7vgn/MacroPad/Software/res/macropad.png

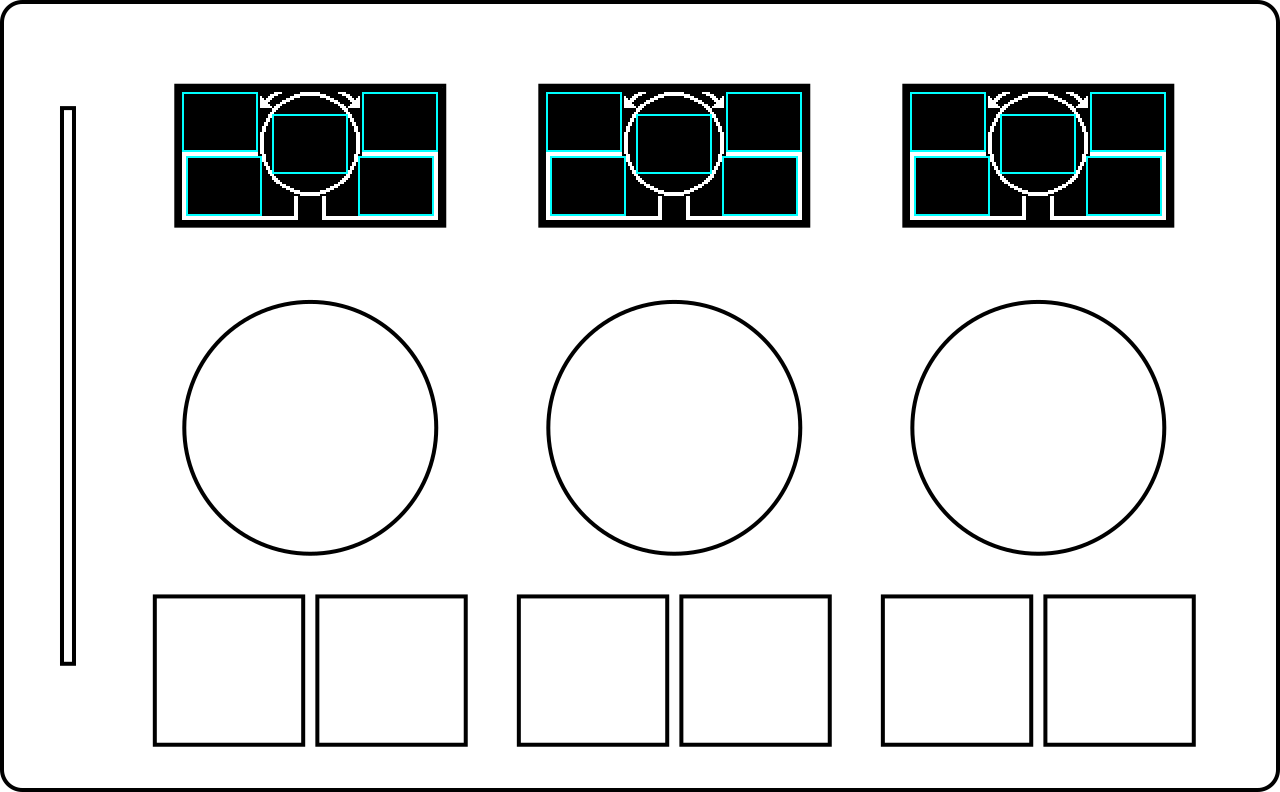
Software/res/macropad.png
