7vgn/MacroPad/Firmware/src/settingstools.cpp

/**
 * \file settingstools.cpp
 * Implementation for settingstools.h
 */

#include<cstdio>
#include"tusb.h"
#include"settingstools.h"

//-----------------------------------------------------------------------------
// Settings implementation

/**
 * \brief Default settings
 * \details These are the result of "macropad-cli -w defaultmp -b default.bin",
 * converted to a C array.
 */
static const uint8_t DEFAULT_SETTINGS[]  = {
  0x00, 0x01, 0x00, 0x4d, 0x6f, 0x75, 0x73, 0x65, 0x00, 0x00, 0x00, 0x00, 0x00, 0x00, 0x00, 0x00,
  0x00, 0x00, 0x00, 0x00, 0x00, 0x00, 0x00, 0x00, 0x00, 0x00, 0x00, 0x00, 0x00, 0x00, 0x00, 0x00,
  0x00, 0x00, 0x00, 0x00, 0x00, 0x00, 0x00, 0x00, 0x00, 0x00, 0x00, 0x00, 0x00, 0x00, 0x00, 0x00,
  0x00, 0x00, 0x00, 0x00, 0x00, 0x00, 0x00, 0x00, 0x00, 0x00, 0x00, 0x00, 0x00, 0x00, 0x00, 0x00,
  0x00, 0x00, 0x00, 0x00, 0x00, 0x00, 0x00, 0x00, 0x00, 0x00, 0x00, 0x00, 0x00, 0x00, 0x00, 0x00,
  0x00, 0x00, 0x00, 0x00, 0x00, 0x00, 0x00, 0x00, 0x00, 0x00, 0x00, 0x00, 0x00, 0x00, 0x00, 0x00,
  0x00, 0x00, 0x00, 0x00, 0x00, 0x00, 0x00, 0x00, 0x00, 0x00, 0x00, 0x00, 0x00, 0x00, 0x00, 0x00,
  0x00, 0x00, 0x00, 0x00, 0x00, 0x00, 0x00, 0x00, 0x00, 0x00, 0x00, 0x00, 0x00, 0x00, 0x00, 0x00,
  0x00, 0x00, 0x00, 0x00, 0x00, 0x00, 0x00, 0x00, 0x00, 0x00, 0x00, 0x00, 0x00, 0x00, 0x00, 0x00,
  0x00, 0x00, 0x00, 0x00, 0x00, 0x00, 0x00, 0x00, 0x00, 0x00, 0x00, 0x00, 0x00, 0x00, 0x00, 0x00,
  0x00, 0x00, 0x00, 0x00, 0x00, 0x00, 0x00, 0x00, 0x00, 0x00, 0x00, 0x00, 0x00, 0x00, 0x00, 0x00,
  0x00, 0x00, 0x00, 0x00, 0x00, 0x00, 0x00, 0x00, 0x00, 0x00, 0x00, 0x00, 0x00, 0x00, 0x00, 0x00,
  0x00, 0x00, 0x00, 0x00, 0x00, 0x00, 0x00, 0x00, 0x00, 0x00, 0x00, 0x00, 0x00, 0x00, 0x00, 0x00,
  0x00, 0x00, 0x00, 0x00, 0x00, 0x00, 0x00, 0x00, 0x00, 0x00, 0x00, 0x00, 0x00, 0x00, 0x00, 0x00,
  0x00, 0x00, 0x00, 0x00, 0x00, 0x00, 0x00, 0x00, 0x00, 0x00, 0x00, 0x00, 0x00, 0x00, 0x00, 0x00,
  0x00, 0x00, 0x00, 0x00, 0x00, 0x00, 0x00, 0x00, 0x00, 0x00, 0x00, 0x00, 0x00, 0x00, 0x00, 0x00,
  0x00, 0x00, 0x00, 0x00, 0x00, 0x00, 0x00, 0x00, 0x00, 0x00, 0x00, 0x00, 0x00, 0x00, 0x00, 0x00,
  0x00, 0x00, 0x00, 0x00, 0x00, 0x00, 0x00, 0x00, 0x00, 0x00, 0x00, 0x00, 0x00, 0x00, 0x00, 0x00,
  0x00, 0x00, 0x00, 0x00, 0x00, 0x00, 0x00, 0x00, 0x00, 0x00, 0x00, 0x00, 0x00, 0x00, 0x00, 0x00,
  0x00, 0x00, 0x00, 0x00, 0x00, 0x00, 0x00, 0x00, 0x00, 0x00, 0x00, 0x00, 0x00, 0x00, 0x00, 0x00,
  0x00, 0x00, 0x00, 0x00, 0x00, 0x00, 0x00, 0x00, 0x00, 0x00, 0x00, 0x00, 0x00, 0x00, 0x00, 0x00,
  0x00, 0x00, 0x00, 0x00, 0x00, 0x00, 0x00, 0x00, 0x00, 0x0e, 0x00, 0x00, 0x00, 0x00, 0x00, 0x00,
  0x00, 0x00, 0x00, 0x00, 0x00, 0x00, 0x00, 0x00, 0x80, 0x3f, 0x00, 0x00, 0x00, 0x00, 0x00, 0x00,
  0x00, 0x00, 0x00, 0x00, 0x00, 0x00, 0x00, 0x00, 0xc0, 0x3f, 0x00, 0xf0, 0x1f, 0x00, 0x00, 0x00,
  0x00, 0x00, 0x00, 0x00, 0x00, 0x00, 0x00, 0x00, 0xe0, 0x7f, 0x00, 0x0f, 0xe0, 0x00, 0x00, 0x00,
  0x00, 0x00, 0x00, 0x00, 0x00, 0x00, 0x00, 0x00, 0xf0, 0xff, 0x80, 0x00, 0x00, 0x07, 0x00, 0x00,
  0x04, 0x00, 0x00, 0x00, 0x00, 0x00, 0x00, 0x00, 0xf8, 0xff, 0x61, 0x00, 0x00, 0x08, 0x00, 0x00,
  0x04, 0x00, 0x00, 0x00, 0x00, 0x00, 0x00, 0x00, 0xfc, 0xff, 0x1b, 0x00, 0x00, 0x10, 0x00, 0x00,
  0x04, 0x00, 0x00, 0x00, 0x00, 0x00, 0x00, 0x00, 0xfe, 0xff, 0x0f, 0x00, 0x00, 0x20, 0x00, 0x00,
  0x04, 0x00, 0x00, 0x00, 0x00, 0x00, 0x00, 0x00, 0xe7, 0xff, 0x0c, 0x00, 0x00, 0x20, 0x00, 0x00,
  0x04, 0x00, 0x00, 0x00, 0x00, 0x00, 0x00, 0x80, 0xc7, 0x7f, 0x1c, 0x00, 0x00, 0x40, 0x00, 0x00,
  0x02, 0x00, 0x00, 0x00, 0x00, 0x00, 0x00, 0xc0, 0x8f, 0x3f, 0x3e, 0x00, 0x00, 0x40, 0x00, 0x00,
  0x01, 0x00, 0x00, 0x00, 0x00, 0x00, 0x00, 0xe0, 0x1f, 0x1f, 0x7f, 0x00, 0x00, 0x80, 0x00, 0x00,
  0x01, 0x00, 0x00, 0x00, 0x00, 0x00, 0x00, 0xf0, 0x3f, 0x8e, 0xff, 0x00, 0x00, 0x80, 0x00, 0x80,
  0x00, 0x00, 0x00, 0x00, 0x00, 0x00, 0x00, 0xf0, 0x7f, 0xc4, 0xff, 0x01, 0x00, 0x00, 0x01, 0x40,
  0x00, 0x00, 0x00, 0x00, 0x00, 0x00, 0x00, 0xf8, 0xff, 0xe0, 0xff, 0x03, 0x00, 0x00, 0x02, 0x38,
  0x00, 0x00, 0x00, 0x00, 0x00, 0x00, 0x00, 0xfc, 0xff, 0xf1, 0xff, 0x03, 0x00, 0x00, 0x04, 0x06,
  0x00, 0x00, 0x00, 0x00, 0x00, 0x00, 0x00, 0xfe, 0xff, 0xe3, 0xff, 0x03, 0x00, 0x00, 0xf8, 0x01,
  0x00, 0x00, 0x00, 0x00, 0x00, 0x00, 0x00, 0xfe, 0xff, 0xc7, 0xff, 0x03, 0x00, 0x00, 0x00, 0x00,
  0x00, 0x00, 0x00, 0x00, 0x00, 0x00, 0x00, 0xff, 0xff, 0x8f, 0xff, 0x01, 0x00, 0x00, 0x00, 0x00,
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
};

void makeDefaultSettings(Settings& settings)
{
	memcpy(&settings, DEFAULT_SETTINGS, sizeof(settings));
}

static bool validateAction(const Settings& settings, const Action& action)
{
	// Make sure profile switching always points to an existing profile
	if(action.type == ActionType::SWITCH_PROFILE
		&& action.switchProfile.index >= NUM_PROFILES)
	{
		printf("Settings invalid: Profile switching actions must point to an existing profile\n");
		return false;
	}
	return true;
}

static bool validateMacro(const Settings& settings, const Macro& macro)
{
	// Make sure the number of steps doesn't exceed the maximum
	if(macro.numSteps > MAX_STEPS_PER_MACRO)
	{
		printf("Settings invalid: Macros cannot have more than %u steps\n", MAX_STEPS_PER_MACRO);
		return false;
	}
	// Validate Actions
	for(uint s = 0; s < macro.numSteps; s++)
		if(!validateAction(settings, macro.steps[s].action))
			return false;
	return true;
}

bool validateSettings(const Settings& settings)
{
	// Check the settings version
	if(settings.version != VERSION)
	{
		printf("Settings invalid: Settings version is %u.%u but firmware version is %u.%u\n", settings.version >> 8, settings.version & 0xff, VERSION >> 8, VERSION & 0xff);
		return false;
	}
	// Make sure the active profile exists
	if(settings.activeProfile >= NUM_PROFILES)
	{
		printf("Settings invalid: Active profile does not exist\n");
		return false;
	}
	// Validate all Actions and Macros
	for(uint p = 0; p < NUM_PROFILES; p++)
	{
		for(uint k = 0; k < 9; k++)
		{
			if(!validateMacro(settings, settings.profiles[p].keys[k].press)) return false;
			if(!validateMacro(settings, settings.profiles[p].keys[k].release)) return false;
			if(!validateMacro(settings, settings.profiles[p].keys[k].longRelease)) return false;
			if(!validateAction(settings, settings.profiles[p].keys[k].hold)) return false;
		}
		for(uint r = 0; r < 3; r++)
		{
			if(!validateMacro(settings, settings.profiles[p].knobs[r].left)) return false;
			if(!validateMacro(settings, settings.profiles[p].knobs[r].right)) return false;
		}
	}
	return true;
}

static void printAction(const Action& action)
{
	switch(action.type)
	{
		case ActionType::NONE:
			printf("Do nothing");
			break;
		case ActionType::SWITCH_PROFILE:
			printf("Switch to Profile %u", action.switchProfile.index + 1);
			break;
		case ActionType::INPUT:
			printf("Keys:");
			for(uint i = 0; i < MAX_KEYS_PER_ACTION; i++)
				if(action.input.keys[i] != HID_KEY_NONE)
					printf(" %u", action.input.keys[i]);
			if(action.input.modifiers & KEYBOARD_MODIFIER_LEFTCTRL) printf(" LCTRL");
			if(action.input.modifiers & KEYBOARD_MODIFIER_LEFTSHIFT) printf(" LSHIFT");
			if(action.input.modifiers & KEYBOARD_MODIFIER_LEFTALT) printf(" LALT");
			if(action.input.modifiers & KEYBOARD_MODIFIER_LEFTGUI) printf(" LWIN");
			if(action.input.modifiers & KEYBOARD_MODIFIER_RIGHTCTRL) printf(" RCTRL");
			if(action.input.modifiers & KEYBOARD_MODIFIER_RIGHTSHIFT) printf(" RSHIFT");
			if(action.input.modifiers & KEYBOARD_MODIFIER_RIGHTALT) printf(" RALT");
			if(action.input.modifiers & KEYBOARD_MODIFIER_RIGHTGUI) printf(" RWIN");
			printf(" Mouse:");
			if(action.input.mouseX != 0) printf(" Move x by %d", action.input.mouseX);
			if(action.input.mouseY != 0) printf(" Move y by %d", action.input.mouseY);
			if(action.input.mouseWheel != 0) printf(" Wheel %d", action.input.mouseWheel);
			if(action.input.mousePan != 0) printf(" Pan %d", action.input.mousePan);
			if(action.input.mouseButtons & MOUSE_BUTTON_LEFT) printf(" Left click");
			if(action.input.mouseButtons & MOUSE_BUTTON_RIGHT) printf(" Right click");
			if(action.input.mouseButtons & MOUSE_BUTTON_MIDDLE) printf(" Middle click");
			if(action.input.mouseButtons & MOUSE_BUTTON_BACKWARD) printf(" Backward");
			if(action.input.mouseButtons & MOUSE_BUTTON_FORWARD) printf(" Forward");
			printf(" CC:");
			if(action.input.consumerControl != 0) printf(" %x", action.input.consumerControl); //FIXME: better output
			printf(" SC:");
			if(action.input.systemControl != 0) printf(" %x", action.input.systemControl); //FIXME: better output
			break;
		default:
			printf("Error: Unknown Action");
	}
}

static void printMacro(const Macro& macro, const char* prefix)
{
	if(macro.numSteps == 0)
		printf("%sEmpty macro\n", prefix);
	else
	{
		printf("%sMacro with %u step(s):\n", prefix, macro.numSteps);
		for(uint s = 0; s < macro.numSteps; s++)
		{
			printf("%s\t", prefix);
			printAction(macro.steps[s].action);
			printf(" (for %ums)\n", macro.steps[s].duration * 10);
		}
	}
}

void printSettings(const Settings& settings)
{
	printf("%u profiles are supported. Profile %u is active.\n", NUM_PROFILES, settings.activeProfile + 1);
	for(uint p = 0; p < NUM_PROFILES; p++)
	{
		printf("Profile %u: \"%s\"\n", p + 1, settings.profiles[p].name);
		for(uint k = 0; k < 9; k++)
		{
			if(k < 6)
				printf("\tKey %u:\n", k + 1);
			else
				printf("\tKnob %u pushbutton:\n", (k - 6) + 1);
			printf("\t\tWhen pressed:\n");
			printMacro(settings.profiles[p].keys[k].press, "\t\t\t");
			printf("\t\tWhen released:\n");
			printMacro(settings.profiles[p].keys[k].release, "\t\t\t");
			printf("\t\tWhile held: ");
			printAction(settings.profiles[p].keys[k].hold);
			printf("\n");
		}
		for(uint r = 0; r < 3; r++)
		{
			printf("\tKnob %u:\n", r + 1);
			printf("\t\tWhen turned left:\n");
			printMacro(settings.profiles[p].knobs[r].left, "\t\t\t");
			printf("\t\tWhen turned right:\n");
			printMacro(settings.profiles[p].knobs[r].right, "\t\t\t");
		}
	}
}

//-----------------------------------------------------------------------------
// MacroList implementation

void MacroList::empty()
{
	for(uint i = 0; i < MAX_ACTIVE_MACROS; i++)
		macros[i].occupied = false;
}

uint MacroList::size() const
{
	uint n = 0;
	for(uint i = 0; i < MAX_ACTIVE_MACROS; i++)
		if(macros[i].occupied)
			n++;
	return n;
}

bool MacroList::isEmpty() const
{
	for(uint i = 0; i < MAX_ACTIVE_MACROS; i++)
		if(macros[i].occupied)
			return false;
	return true;
}

bool MacroList::add(const Macro& macro)
{
	for(uint i = 0; i < MAX_ACTIVE_MACROS; i++)
	{
		if(!macros[i].occupied)
		{
			macros[i].occupied = true;
			macros[i].macro = &macro;
			macros[i].tick = 0;
			return true;
		}
	}
	return false;
}

void MacroList::addToReport(UsbHidInterface* interfaces[], uint numInterfaces, void (*nonInputActionCallback)(const Action&, void*), void* userData)
{
	for(uint i = 0; i < MAX_ACTIVE_MACROS; i++)
	{
		if(!macros[i].occupied)
			continue;
		// By looking at the tick counter, find out which step the macro is currently in
		uint tick = macros[i].tick;
		uint step = 0;
		while(step < macros[i].macro->numSteps && tick >= macros[i].macro->steps[step].duration)
		{
			tick -= macros[i].macro->steps[step].duration;
			step++;
		}
		// Remove Macro from list if it has run its course
		if(step >= macros[i].macro->numSteps)
		{
			macros[i].occupied = false;
			continue;
		}

		// Is this an INPUT-type action?
		if(macros[i].macro->steps[step].action.type == ActionType::INPUT)
		{
			// Add the action from this step to the reports
			for(uint j = 0; j < numInterfaces; j++)
				interfaces[j]->addActionToReport(macros[i].macro->steps[step].action);
		}
		else if(nonInputActionCallback != nullptr)
			// Callback for other actions
			nonInputActionCallback(macros[i].macro->steps[step].action, userData);

		// Increment step counter
		macros[i].tick++;
	}
}
